ljagiello/totem-compass/hardware/totem-v3.5-reference/schematic/totem_sklib.py

from collections import defaultdict
from skidl import Pin, Part, Alias, SchLib, SKIDL, TEMPLATE

from skidl.pin import pin_types

SKIDL_lib_version = '0.0.1'

totem = SchLib(tool=SKIDL).add_parts(*[
        Part(**{ 'name':'USB_C_Receptacle_PowerOnly_6P', 'dest':TEMPLATE, 'tool':SKIDL, 'aliases':Alias({'USB_C_Receptacle_PowerOnly_6P'}), 'ref_prefix':'J', 'fplist':[''], 'footprint':'Connector_USB:USB_C_Receptacle_GCT_USB4135-GF-A_6P_TopMnt_Horizontal', 'keywords':'usb universal serial bus type-C power-only charging-only 6P 6C', 'description':'USB Power-Only 6P Type-C Receptacle connector', 'datasheet':'https://www.usb.org/sites/default/files/documents/usb_type-c.zip', 'pins':[
            Pin(num='A5',name='CC1',func=pin_types.BIDIR,unit=1),
            Pin(num='A9',name='VBUS',func=pin_types.PASSIVE,unit=1),
            Pin(num='A12',name='GND',func=pin_types.PASSIVE,unit=1),
            Pin(num='B5',name='CC2',func=pin_types.BIDIR,unit=1),
            Pin(num='B9',name='VBUS',func=pin_types.PASSIVE,unit=1),
            Pin(num='B12',name='GND',func=pin_types.PASSIVE,unit=1),
            Pin(num='SH',name='SHIELD',func=pin_types.PASSIVE,unit=1)], 'unit_defs':[] }),
        Part(**{ 'name':'R', 'dest':TEMPLATE, 'tool':SKIDL, 'aliases':Alias({'R'}), 'ref_prefix':'R', 'fplist':[''], 'footprint':'Resistor_SMD:R_0603_1608Metric', 'keywords':'R res resistor', 'description':'Resistor', 'datasheet':'', 'pins':[
            Pin(num='1',func=pin_types.PASSIVE,unit=1),
            Pin(num='2',func=pin_types.PASSIVE,unit=1)], 'unit_defs':[] }),
        Part(**{ 'name':'C', 'dest':TEMPLATE, 'tool':SKIDL, 'aliases':Alias({'C'}), 'ref_prefix':'C', 'fplist':[''], 'footprint':'Capacitor_SMD:C_0805_2012Metric', 'keywords':'cap capacitor', 'description':'Unpolarized capacitor', 'datasheet':'', 'pins':[
            Pin(num='1',func=pin_types.PASSIVE,unit=1),
            Pin(num='2',func=pin_types.PASSIVE,unit=1)], 'unit_defs':[] }),
        Part(**{ 'name':'TP4056-42-ESOP8', 'dest':TEMPLATE, 'tool':SKIDL, 'aliases':Alias({'TP4056-42-ESOP8'}), 'ref_prefix':'U', 'fplist':['Package_SO:SOIC-8-1EP_3.9x4.9mm_P1.27mm_EP2.41x3.3mm_ThermalVias'], 'footprint':'Package_SO:SOIC-8-1EP_3.9x4.9mm_P1.27mm_EP2.29x3mm', 'keywords':'lithium-ion lithium-polymer Li-Poly', 'description':'1A Standalone Linear Li-ion/LiPo single-cell battery charger, 4.2V Â±1% charge voltage, VCC = 4.0..8.0V, SOIC-8 (SOP-8)', 'datasheet':'https://www.lcsc.com/datasheet/lcsc_datasheet_2410121619_TOPPOWER-Nanjing-Extension-Microelectronics-TP4056-42-ESOP8_C16581.pdf', 'pins':[
            Pin(num='1',name='TEMP',func=pin_types.INPUT,unit=1),
            Pin(num='2',name='PROG',func=pin_types.PASSIVE,unit=1),
            Pin(num='3',name='GND',func=pin_types.PWRIN,unit=1),
            Pin(num='4',name='V_{CC}',func=pin_types.PWRIN,unit=1),
            Pin(num='5',name='BAT',func=pin_types.PWROUT,unit=1),
            Pin(num='6',name='~{STDBY}',func=pin_types.OPENCOLL,unit=1),
            Pin(num='7',name='~{CHRG}',func=pin_types.OPENCOLL,unit=1),
            Pin(num='8',name='CE',func=pin_types.INPUT,unit=1),
            Pin(num='9',name='EPAD',func=pin_types.PASSIVE,unit=1)], 'unit_defs':[] }),
        Part(**{ 'name':'LED', 'dest':TEMPLATE, 'tool':SKIDL, 'aliases':Alias({'LED'}), 'ref_prefix':'D', 'fplist':[''], 'footprint':'LED_SMD:LED_0603_1608Metric', 'keywords':'LED diode', 'description':'Light emitting diode', 'datasheet':'', 'pins':[
            Pin(num='1',name='K',func=pin_types.PASSIVE,unit=1),
            Pin(num='2',name='A',func=pin_types.PASSIVE,unit=1)], 'unit_defs':[] }),
        Part(**{ 'name':'Conn_01x02', 'dest':TEMPLATE, 'tool':SKIDL, 'aliases':Alias({'Conn_01x02'}), 'ref_prefix':'J', 'fplist':[''], 'footprint':'Connector_JST:JST_PH_S2B-PH-K_1x02_P2.00mm_Horizontal', 'keywords':'connector', 'description':'Generic connector, single row, 01x02, script generated (kicad-library-utils/schlib/autogen/connector/)', 'datasheet':'', 'pins':[
            Pin(num='1',name='Pin_1',func=pin_types.PASSIVE,unit=1),
            Pin(num='2',name='Pin_2',func=pin_types.PASSIVE,unit=1)], 'unit_defs':[] }),
        Part(**{ 'name':'SW_Push', 'dest':TEMPLATE, 'tool':SKIDL, 'aliases':Alias({'SW_Push'}), 'ref_prefix':'SW', 'fplist':[''], 'footprint':'Button_Switch_SMD:SW_SPST_PTS645Sx43SMTR92', 'keywords':'switch normally-open pushbutton push-button', 'description':'Push button switch, generic, two pins', 'datasheet':'', 'pins':[
            Pin(num='1',name='1',func=pin_types.PASSIVE),
            Pin(num='2',name='2',func=pin_types.PASSIVE)], 'unit_defs':[] }),
        Part(**{ 'name':'AO3401A', 'dest':TEMPLATE, 'tool':SKIDL, 'aliases':Alias({'AO3401A'}), 'ref_prefix':'Q', 'fplist':['Package_TO_SOT_SMD:SOT-23', 'Package_TO_SOT_SMD:SOT-23'], 'footprint':'Package_TO_SOT_SMD:SOT-23', 'keywords':'P-Channel MOSFET', 'description':'-4.0A Id, -30V Vds, P-Channel MOSFET, SOT-23', 'datasheet':'http://www.aosmd.com/pdfs/datasheet/AO3401A.pdf', 'pins':[
            Pin(num='1',name='G',func=pin_types.INPUT,unit=1),
            Pin(num='2',name='S',func=pin_types.PASSIVE,unit=1),
            Pin(num='3',name='D',func=pin_types.PASSIVE,unit=1)], 'unit_defs':[] }),
        Part(**{ 'name':'2N7002', 'dest':TEMPLATE, 'tool':SKIDL, 'aliases':Alias({'2N7002'}), 'ref_prefix':'Q', 'fplist':['', 'Package_TO_SOT_SMD:SOT-23'], 'footprint':'Package_TO_SOT_SMD:SOT-23', 'keywords':'N-Channel Switching MOSFET', 'description':'0.115A Id, 60V Vds, N-Channel MOSFET, SOT-23', 'datasheet':'https://www.onsemi.com/pub/Collateral/NDS7002A-D.PDF', 'pins':[
            Pin(num='1',name='G',func=pin_types.INPUT,unit=1),
            Pin(num='2',name='S',func=pin_types.PASSIVE,unit=1),
            Pin(num='3',name='D',func=pin_types.PASSIVE,unit=1)], 'unit_defs':[] }),
        Part(**{ 'name':'1N4148W', 'dest':TEMPLATE, 'tool':SKIDL, 'aliases':Alias({'1N4148W'}), 'ref_prefix':'D', 'fplist':['Diode_THT:D_DO-41_SOD81_P10.16mm_Horizontal', 'Diode_SMD:D_SOD-123'], 'footprint':'Diode_SMD:D_SOD-123', 'keywords':'diode', 'description':'75V 0.15A Fast Switching Diode, SOD-123', 'datasheet':'https://www.vishay.com/docs/85748/1n4148w.pdf', 'pins':[
            Pin(num='1',name='K',func=pin_types.PASSIVE,unit=1),
            Pin(num='2',name='A',func=pin_types.PASSIVE,unit=1)], 'unit_defs':[] }),
        Part(**{ 'name':'BAT54W', 'dest':TEMPLATE, 'tool':SKIDL, 'aliases':Alias({'BAT54W'}), 'ref_prefix':'D', 'fplist':['Package_TO_SOT_SMD:SOT-323_SC-70'], 'footprint':'Package_TO_SOT_SMD:SOT-323_SC-70', 'keywords':'schottky diode', 'description':'Schottky barrier diode, SOT-323', 'datasheet':'https://assets.nexperia.com/documents/data-sheet/BAT54W_SER.pdf', 'pins':[
            Pin(num='1',name='A',func=pin_types.PASSIVE,unit=1),
            Pin(num='2',name='NC',func=pin_types.NOCONNECT,unit=1),
            Pin(num='3',name='K',func=pin_types.PASSIVE,unit=1)], 'unit_defs':[] }),
        Part(**{ 'name':'AP2112K-3.3', 'dest':TEMPLATE, 'tool':SKIDL, 'aliases':Alias({'AP2112K-3.3'}), 'ref_prefix':'U', 'fplist':['Package_TO_SOT_SMD:SOT-23-5', 'Package_TO_SOT_SMD:SOT-23-5'], 'footprint':'Package_TO_SOT_SMD:SOT-23-5', 'keywords':'linear regulator ldo fixed positive', 'description':'600mA low dropout linear regulator, with enable pin, 3.8V-6V input voltage range, 3.3V fixed positive output, SOT-23-5', 'datasheet':'https://www.diodes.com/assets/Datasheets/AP2112.pdf', 'pins':[
            Pin(num='1',name='VIN',func=pin_types.PWRIN,unit=1),
            Pin(num='2',name='GND',func=pin_types.PWRIN,unit=1),
            Pin(num='3',name='EN',func=pin_types.INPUT,unit=1),
            Pin(num='4',name='NC',func=pin_types.NOCONNECT,unit=1),
            Pin(num='5',name='VOUT',func=pin_types.PWROUT,unit=1)], 'unit_defs':[] }),
        Part(**{ 'name':'ESP32-WROOM-32E', 'dest':TEMPLATE, 'tool':SKIDL, 'aliases':Alias({'ESP32-WROOM-32E'}), 'ref_prefix':'U', 'fplist':['RF_Module:ESP32-WROOM-32E'], 'footprint':'RF_Module:ESP32-WROOM-32E', 'keywords':'RF Radio BT ESP ESP32 Espressif onboard PCB antenna', 'description':'RF Module, ESP32-D0WD-V3 SoC, without PSRAM, Wi-Fi 802.11b/g/n, Bluetooth, BLE, 32-bit, 2.7-3.6V, onboard antenna, SMD', 'datasheet':'https://www.espressif.com/sites/default/files/documentation/esp32-wroom-32e_esp32-wroom-32ue_datasheet_en.pdf', 'pins':[
            Pin(num='2',name='VDD',func=pin_types.PWRIN,unit=1),
            Pin(num='3',name='EN',func=pin_types.INPUT,unit=1),
            Pin(num='4',name='SENSOR_VP',func=pin_types.INPUT,unit=1),
            Pin(num='5',name='SENSOR_VN',func=pin_types.INPUT,unit=1),
            Pin(num='6',name='IO34',func=pin_types.INPUT,unit=1),
            Pin(num='7',name='IO35',func=pin_types.INPUT,unit=1),
            Pin(num='8',name='IO32',func=pin_types.BIDIR,unit=1),
            Pin(num='9',name='IO33',func=pin_types.BIDIR,unit=1),
            Pin(num='10',name='IO25',func=pin_types.BIDIR,unit=1),
            Pin(num='11',name='IO26',func=pin_types.BIDIR,unit=1),
            Pin(num='12',name='IO27',func=pin_types.BIDIR,unit=1),
            Pin(num='13',name='IO14',func=pin_types.BIDIR,unit=1),
            Pin(num='14',name='IO12',func=pin_types.BIDIR,unit=1),
            Pin(num='16',name='IO13',func=pin_types.BIDIR,unit=1),
            Pin(num='17',name='NC',func=pin_types.NOCONNECT,unit=1),
            Pin(num='18',name='NC',func=pin_types.NOCONNECT,unit=1),
            Pin(num='19',name='NC',func=pin_types.NOCONNECT,unit=1),
            Pin(num='20',name='NC',func=pin_types.NOCONNECT,unit=1),
            Pin(num='21',name='NC',func=pin_types.NOCONNECT,unit=1),
            Pin(num='22',name='NC',func=pin_types.NOCONNECT,unit=1),
            Pin(num='23',name='IO15',func=pin_types.BIDIR,unit=1),
            Pin(num='24',name='IO2',func=pin_types.BIDIR,unit=1),
            Pin(num='25',name='IO0',func=pin_types.BIDIR,unit=1),
            Pin(num='26',name='IO4',func=pin_types.BIDIR,unit=1),
            Pin(num='27',name='IO16',func=pin_types.BIDIR,unit=1),
            Pin(num='28',name='IO17',func=pin_types.BIDIR,unit=1),
            Pin(num='29',name='IO5',func=pin_types.BIDIR,unit=1),
            Pin(num='30',name='IO18',func=pin_types.BIDIR,unit=1),
            Pin(num='31',name='IO19',func=pin_types.BIDIR,unit=1),
            Pin(num='32',name='NC',func=pin_types.NOCONNECT,unit=1),
            Pin(num='33',name='IO21',func=pin_types.BIDIR,unit=1),
            Pin(num='34',name='RXD0/IO3',func=pin_types.BIDIR,unit=1),
            Pin(num='35',name='TXD0/IO1',func=pin_types.BIDIR,unit=1),
            Pin(num='36',name='IO22',func=pin_types.BIDIR,unit=1),
            Pin(num='37',name='IO23',func=pin_types.BIDIR,unit=1),
            Pin(num='[1,15,38,39]',name='GND',func=pin_types.PWRIN,unit=1)], 'unit_defs':[] }),
        Part(**{ 'name':'TestPoint', 'dest':TEMPLATE, 'tool':SKIDL, 'aliases':Alias({'TestPoint'}), 'ref_prefix':'TP', 'fplist':[''], 'footprint':'TestPoint:TestPoint_Pad_D1.0mm', 'keywords':'test point tp', 'description':'test point', 'datasheet':'', 'pins':[
            Pin(num='1',name='1',func=pin_types.PASSIVE,unit=1)], 'unit_defs':[] }),
        Part(**{ 'name':'MAX-M10S', 'dest':TEMPLATE, 'tool':SKIDL, 'aliases':Alias({'MAX-M10S'}), 'ref_prefix':'U', 'fplist':['RF_GPS:ublox_MAX'], 'footprint':'RF_GPS:ublox_MAX', 'keywords':'ublox GPS GNSS module', 'description':'GNSS Module MAX M10, VCC 1.65V to 3.6V', 'datasheet':'https://content.u-blox.com/sites/default/files/MAX-M10S_DataSheet_UBX-20035208.pdf', 'pins':[
            Pin(num='1',name='GND',func=pin_types.PWRIN,unit=1),
            Pin(num='2',name='TXD',func=pin_types.OUTPUT,unit=1),
            Pin(num='3',name='RXD',func=pin_types.INPUT,unit=1),
            Pin(num='4',name='TIMEPULSE',func=pin_types.OUTPUT,unit=1),
            Pin(num='5',name='EXTINT',func=pin_types.INPUT,unit=1),
            Pin(num='6',name='V_BCKP',func=pin_types.PWRIN,unit=1),
            Pin(num='7',name='VCC_IO',func=pin_types.PWRIN,unit=1),
            Pin(num='8',name='VCC',func=pin_types.PWRIN,unit=1),
            Pin(num='9',name='~{RESET}',func=pin_types.INPUT,unit=1),
            Pin(num='10',name='GND',func=pin_types.PASSIVE,unit=1),
            Pin(num='11',name='RF_IN',func=pin_types.INPUT,unit=1),
            Pin(num='12',name='GND',func=pin_types.PASSIVE,unit=1),
            Pin(num='13',name='LNA_EN',func=pin_types.OUTPUT,unit=1),
            Pin(num='14',name='VCC_RF',func=pin_types.PWROUT,unit=1),
            Pin(num='15',name='VIO_SEL',func=pin_types.INPUT,unit=1),
            Pin(num='16',name='SDA',func=pin_types.BIDIR,unit=1),
            Pin(num='17',name='SCL',func=pin_types.INPUT,unit=1),
            Pin(num='18',name='~{SAFEBOOT}',func=pin_types.INPUT,unit=1)], 'unit_defs':[] }),
        Part(**{ 'name':'Conn_Coaxial', 'dest':TEMPLATE, 'tool':SKIDL, 'aliases':Alias({'Conn_Coaxial'}), 'ref_prefix':'J', 'fplist':[''], 'footprint':'Connector_Coaxial:U.FL_Hirose_U.FL-R-SMT-1_Vertical', 'keywords':'BNC SMA SMB SMC LEMO coaxial connector CINCH RCA MCX MMCX U.FL UMRF', 'description':'coaxial connector (BNC, SMA, SMB, SMC, Cinch/RCA, LEMO, ...)', 'datasheet':'', 'pins':[
            Pin(num='1',name='In',func=pin_types.PASSIVE,unit=1),
            Pin(num='2',name='Ext',func=pin_types.PASSIVE,unit=1)], 'unit_defs':[] }),
        Part(**{ 'name':'LSM6DSM', 'dest':TEMPLATE, 'tool':SKIDL, 'aliases':Alias({'LSM6DSM'}), 'ref_prefix':'U', 'fplist':['Package_LGA:LGA-14_3x2.5mm_P0.5mm_LayoutBorder3x4y'], 'footprint':'Package_LGA:LGA-14_3x2.5mm_P0.5mm_LayoutBorder3x4y', 'keywords':'Accelerometer Gyroscope MEMS', 'description':'I2C/SPI, iNEMO inertial module: always-on 3D accelerometer and 3D gyroscope, with auxiliary SPI, 1.71V to 3.6V VCC', 'datasheet':'https://www.st.com/resource/en/datasheet/lsm6dsm.pdf', 'pins':[
            Pin(num='1',name='SDO/SA0',func=pin_types.BIDIR,unit=1),
            Pin(num='2',name='SDX',func=pin_types.BIDIR,unit=1),
            Pin(num='3',name='SCX',func=pin_types.INPUT,unit=1),
            Pin(num='4',name='INT1',func=pin_types.OUTPUT,unit=1),
            Pin(num='5',name='VDDIO',func=pin_types.PWRIN,unit=1),
            Pin(num='6',name='GND',func=pin_types.PWRIN,unit=1),
            Pin(num='7',name='GND',func=pin_types.PASSIVE,unit=1),
            Pin(num='8',name='VDD',func=pin_types.PWRIN,unit=1),
            Pin(num='9',name='INT2',func=pin_types.OUTPUT,unit=1),
            Pin(num='10',name='OCS_Aux',func=pin_types.PASSIVE,unit=1),
            Pin(num='11',name='SDO_Aux',func=pin_types.BIDIR,unit=1),
            Pin(num='12',name='CS',func=pin_types.INPUT,unit=1),
            Pin(num='13',name='SCL',func=pin_types.INPUT,unit=1),
            Pin(num='14',name='SDA',func=pin_types.BIDIR,unit=1)], 'unit_defs':[] }),
        Part(**{ 'name':'LIS2MDL', 'dest':TEMPLATE, 'tool':SKIDL, 'aliases':Alias({'LIS2MDL'}), 'ref_prefix':'U', 'fplist':['Package_LGA:LGA-12_2x2mm_P0.5mm'], 'footprint':'Package_LGA:LGA-12_2x2mm_P0.5mm', 'keywords':'digital magnetometer', 'description':'Ultra-low-power, 3-axis digital output magnetometer, LGA-12', 'datasheet':'https://www.st.com/resource/en/datasheet/lis2mdl.pdf', 'pins':[
            Pin(num='1',name='SCL/SPC',func=pin_types.INPUT,unit=1),
            Pin(num='2',name='NC',func=pin_types.NOCONNECT,unit=1),
            Pin(num='3',name='~{CS}',func=pin_types.INPUT,unit=1),
            Pin(num='4',name='SDA/SDI/SDO',func=pin_types.BIDIR,unit=1),
            Pin(num='5',name='C1',func=pin_types.PWROUT,unit=1),
            Pin(num='6',name='GND',func=pin_types.PWRIN,unit=1),
            Pin(num='7',name='DRDY',func=pin_types.OUTPUT,unit=1),
            Pin(num='8',name='GND',func=pin_types.PASSIVE,unit=1),
            Pin(num='9',name='Vdd',func=pin_types.PWRIN,unit=1),
            Pin(num='10',name='Vdd_IO',func=pin_types.PWRIN,unit=1),
            Pin(num='11',name='NC',func=pin_types.NOCONNECT,unit=1),
            Pin(num='12',name='NC',func=pin_types.NOCONNECT,unit=1)], 'unit_defs':[] }),
        Part(**{ 'name':'WS2812B-2020', 'dest':TEMPLATE, 'tool':SKIDL, 'aliases':Alias({'WS2812B-2020'}), 'ref_prefix':'D', 'fplist':['LED_SMD:LED_WS2812B-2020_PLCC4_2.0x2.0mm'], 'footprint':'totem:LED_XL-1515RGBC-WS2812B', 'keywords':'RGB LED NeoPixel Nano addressable', 'description':'RGB LED with integrated controller, 2.0 x 2.0 mm, 12 mA', 'datasheet':'https://cdn-shop.adafruit.com/product-files/4684/4684_WS2812B-2020_V1.3_EN.pdf', 'pins':[
            Pin(num='1',name='DOUT',func=pin_types.OUTPUT,unit=1),
            Pin(num='2',name='VSS',func=pin_types.PWRIN,unit=1),
            Pin(num='3',name='DIN',func=pin_types.INPUT,unit=1),
            Pin(num='4',name='VDD',func=pin_types.PWRIN,unit=1)], 'unit_defs':[] }),
        Part(**{ 'name':'Microphone_Condenser', 'dest':TEMPLATE, 'tool':SKIDL, 'aliases':Alias({'Microphone_Condenser'}), 'ref_prefix':'MK', 'fplist':[''], 'footprint':'totem:CUI_CMC-4013-SMT_RingGap', 'keywords':'capacitance condenser microphone', 'description':'Condenser microphone', 'datasheet':'', 'pins':[
            Pin(num='1',name='-',func=pin_types.PASSIVE,unit=1),
            Pin(num='2',name='+',func=pin_types.PASSIVE,unit=1)], 'unit_defs':[] })])
